athrvchvn/TLMMS/docs/handbook/chapters/ch10_security_model.tex

%% Chapter 10 — Security Model
\chapter{Security Model}
\label{ch:security}

\section{Threat Model}

MMS V2 is deployed in a university lab on a trusted LAN. The threat model assumes:

\begin{itemize}[leftmargin=1.5em]
    \item \textbf{Insider threat (student)}: A student may attempt to use a machine they are not authorised for. A student may attempt to stay on a machine beyond the session limit.
    \item \textbf{Card theft or loss}: A student's RFID card may be stolen or lost. The attacker would attempt to use it to gain machine access.
    \item \textbf{Card forgery}: An attacker may attempt to create a fake RFID card with crafted block data.
    \item \textbf{Physical access to node}: An attacker may attempt to physically tamper with the ESP32 node.
    \item \textbf{WiFi LAN attacker}: An attacker on the same WiFi may attempt to inject MQTT messages.
\end{itemize}

\textbf{Out of scope}: Remote internet attackers (Firebase security rules handle this), state-level adversaries, physical break-ins.

\section{Security Controls}

\section{Attack Surface}

\begin{longtable}{L{3.5cm}L{5cm}L{5.5cm}}
\toprule
\textbf{Surface} & \textbf{Primary risk} & \textbf{Control} \\
\midrule
\endhead
RFID card & Lost card, cloned card, modified permissions & Per-card sector key, revocation list, coordinator incident process \\
ESP32 node & Flash extraction, relay tampering, malicious firmware & Physical enclosure, secrets discipline, OTA gate, relay-off boot default \\
MQTT LAN & Command injection, status spoofing, message sniffing & Lab network trust boundary; enable authentication and ACLs for hardened deployment \\
Raspberry Pi & Firebase Admin SDK compromise, bridge outage & Least shared access, systemd watchdog, SD backup, health endpoint \\
Firebase & Admin account takeover, rule misconfiguration & Firebase Auth, Firestore role documents, sessions write locked to Admin SDK \\
Kiosk station & Unauthorized card issuance & Restrict physical access, keep master key off shared drives, audit issued cards \\
\bottomrule
\caption{MMS V2 attack surface review}
\label{tab:attack_surface}
\end{longtable}

\subsection{Card Forgery Prevention}

Each card's Sector 1 is protected by a unique 6-byte key derived as:
\[
\text{sector\_key}[6] = \text{HMAC-SHA256}(\text{master\_key},\, \text{uid\_hex})[0..5]
\]

An attacker cannot read Sector 1 data without knowing the master key. An attacker cannot write to Sector 1 without the sector key. Since the sector key is derived from the card's own UID and the master key, creating a forged card with a new UID requires knowledge of the master key.

The MFRC522 \textbf{never returns Key A on a read} --- even with authenticated access. So compromising one card does not reveal the sector key for another card.

\subsection{MIFARE Classic and Crypto-1 Limitations}

MMS V2 uses MIFARE Classic 1K cards because they are inexpensive, widely available, and supported by the MFRC522 reader used in the deployed hardware. This choice has a known security cost: MIFARE Classic uses the Crypto-1 stream cipher, which is publicly broken. A determined attacker with the right tools can recover keys or clone cards more easily than they could with modern smart-card technology.

The V2 card design reduces casual forgery by deriving a unique sector key from the card UID and a private master key. This prevents a student from simply editing visible card data with default keys. It does \textbf{not} make MIFARE Classic cryptographically strong. A high-skill attacker with physical access to a valid card and time to attack Crypto-1 remains in scope as a residual risk.

\begin{riskbox}{Security Boundary}
Treat MIFARE Classic cards as a practical lab-access token, not a high-assurance identity credential. The system is appropriate for supervised workshop access control. It should not be reused for payments, room access, hostel access, exam identity, or other high-value authorization.
\end{riskbox}

\subsection{Card Cloning Risk}

Card cloning can happen in two ways:
\begin{itemize}[leftmargin=1.5em]
    \item \textbf{UID cloning}: some magic cards can emulate another card UID. If the attacker also has valid Sector 1 contents, the node may treat the clone as the original card.
    \item \textbf{Sector recovery}: Crypto-1 attacks may recover the sector key for a card, allowing its protected data to be copied.
\end{itemize}

Mitigations are operational as much as technical: revoke lost cards quickly, keep cards physically controlled, do not publish the master key, and review suspicious repeated sessions. For high-value machines or unsupervised labs, migrate to DESFire before relying on card-only access.

\subsection{Revocation}

Lost or stolen cards are revoked via the web app. Revocation propagates to all nodes via MQTT within seconds. Revoked card UIDs are stored in LittleFS on each node, so revocation works even if the MQTT broker goes down (until the next reconnect, nodes use their cached revocation list).

\textbf{Limitation:} A revoked card that is used while a node is offline may be accepted until the node reconnects. This is a known trade-off in favour of offline availability.

\subsection{Admin Web App}

\begin{itemize}[leftmargin=1.5em]
    \item Firebase Authentication protects admin login (email/password)
    \item Firestore security rules check \texttt{/admins/\{uid\}} and \texttt{/super\_admins/\{uid\}} on every client request
    \item Sessions collection has \texttt{allow write: if false} --- only the bridge (Admin SDK) can write sessions, preventing session forgery from the client
    \item Super admin privileges required for OTA and admin management
\end{itemize}

\subsection{MQTT Security}

In the default deployment, MQTT uses \texttt{allow\_anonymous true}. This is acceptable in a physically secure lab LAN where all connected devices are managed. For hardened deployments:

\begin{itemize}[leftmargin=1.5em]
    \item Enable MQTT password authentication (see Section~\ref{sec:mqtt_auth})
    \item Add per-node ACLs to restrict which topics each node can publish/subscribe to
    \item Use TLS on MQTT (port 8883) if the lab network is untrusted
\end{itemize}

\subsection{Secrets Management}

Sensitive secrets are never committed to version control. The \texttt{.gitignore} covers:
\begin{itemize}[leftmargin=1.5em,noitemsep]
    \item \texttt{v2/access\_node/secrets.h} (WiFi credentials, master key)
    \item \texttt{v2/kiosk\_station/station\_writer/secrets\_station.h} (master key)
    \item \texttt{v2/kiosk\_station/secrets.py} (master key)
    \item \texttt{v2/rpi\_bridge/service-account.json} (Firebase Admin SDK key)
    \item \texttt{v2/web\_app/lab-access-nexus-main/.env} (Firebase client config)
\end{itemize}

\subsection{Firmware Security}

\begin{itemize}[leftmargin=1.5em]
    \item OTA firmware is downloaded from Firebase Storage (HTTPS). \texttt{esp\_https\_ota()} validates the TLS certificate.
    \item The dual-partition OTA scheme with rollback prevents a bad firmware update from permanently bricking a node.
    \item The 30-second hardware watchdog ensures the node restarts in case of firmware hang, preventing a machine from being left in relay-ON state indefinitely.
    \item Relay GPIO is driven LOW before \texttt{pinMode(OUTPUT)}, ensuring the relay is OFF during boot regardless of the GPIO's default state.
\end{itemize}

\section{DESFire Migration Path}

DESFire EV2/EV3 cards provide modern mutual authentication and stronger application separation than MIFARE Classic. The migration should be treated as a hardware-and-firmware project, not a card swap.

\begin{enumerate}[leftmargin=1.5em]
    \item Select a DESFire-capable reader module and validate ESP32 library support.
    \item Define a new card application layout with separate identity and permission files.
    \item Implement dual-reader or dual-card support during transition if existing cards must keep working.
    \item Update kiosk issuance to create DESFire applications and diversify keys per card.
    \item Add a schema version gate so nodes can reject old Classic cards after the cutover date.
    \item Re-issue all active users and record the migration in the ADR table.
\end{enumerate}

\begin{table}[H]
\centering
\caption{Classic-to-DESFire migration comparison}
\begin{tabular}{L{4cm}L{4.5cm}L{5cm}}
\toprule
\textbf{Area} & \textbf{MIFARE Classic V2} & \textbf{DESFire target} \\
\midrule
Cryptography & Crypto-1, known weak & AES-based mutual authentication \\
Reader & MFRC522 & PN532, PN5180, or equivalent DESFire-capable reader \\
Card identity & UID plus protected sector data & Application/file-level credential design \\
Transition effort & Already deployed & Requires reader, firmware, kiosk, and procurement changes \\
\bottomrule
\end{tabular}
\end{table}

\section{Security Assumptions and Limitations}

\begin{table}[H]
\centering
\caption{Security Assumptions and Limitations}
\begin{tabular}{L{5cm}L{9cm}}
\toprule
\textbf{Assumption / Limitation} & \textbf{Details} \\
\midrule
Master key is secure & If the master key is stolen, all cards can be forged. The key must be stored in a password manager, not in plaintext on a shared drive. \\
Lab WiFi is trusted & MQTT uses no encryption. A packet sniffer on the same WiFi can read MQTT messages (but not master key or Firebase credentials, which are never in MQTT). \\
Revocation is not instant & Offline nodes cannot revoke cards immediately. A stolen card may work for minutes to hours if the affected node is offline. \\
Physical node security & An attacker with physical access to the ESP32 can read flash, extract master key. Epoxy potting of the PCB mitigates this. \\
PIN not verified at machine (V2) & Card tap alone is sufficient. A thief with a stolen card can use any permitted machine. Revocation is the mitigation. \\
Firebase free tier & Data stored in Google Cloud. Subject to Google's terms of service. For highly sensitive data, consider self-hosted alternatives. \\
\bottomrule
\end{tabular}
\end{table}

\section{Security Checklist for Future Maintainers}

Before deploying any change, verify:
\begin{itemize}[leftmargin=1.5em]
    \item \texttt{secrets.h}, \texttt{secrets.py}, \texttt{secrets\_station.h} are NOT committed to git (\texttt{git status} should not show them)
    \item Firestore rules still have \texttt{allow write: if false} on the \texttt{sessions} collection
    \item RTDB rules protect \texttt{nodes} and \texttt{revoked} paths from unauthenticated writes
    \item New admin accounts are added to Firestore \texttt{/admins} or \texttt{/super\_admins} only --- do not grant access by adding to Firebase Auth alone
    \item OTA firmware URL uses HTTPS (Firebase Storage URLs always do)
    \item Master key backup is current and stored securely
\end{itemize}
