athrvchvn/TLMMS/handbook2.0/media/photo_02.jpeg

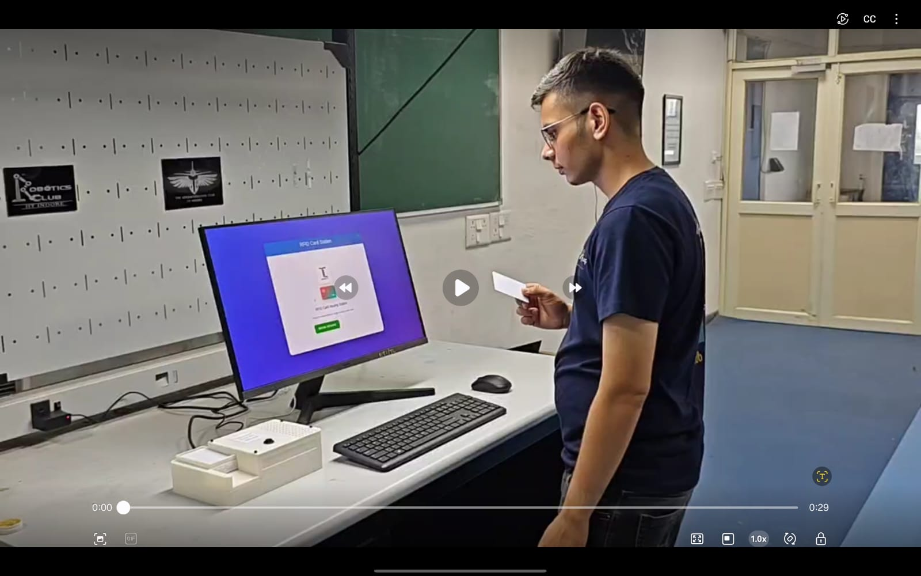
handbook2.0/media/photo_02.jpeg
