athrvchvn/TLMMS/handbook2.0/media/photo_04.jpeg

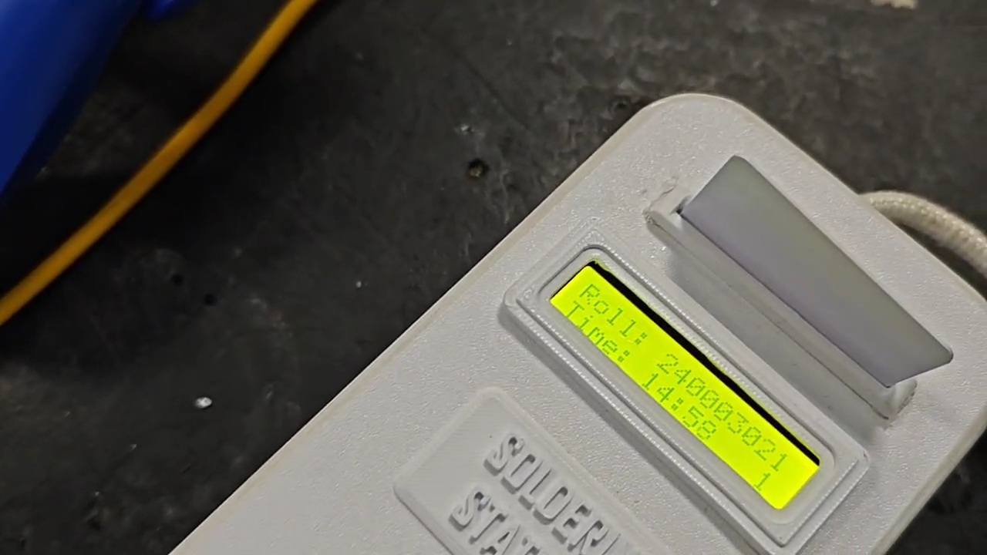
handbook2.0/media/photo_04.jpeg
