athrvchvn/TLMMS/handbook2.0/media/photo_06.jpeg

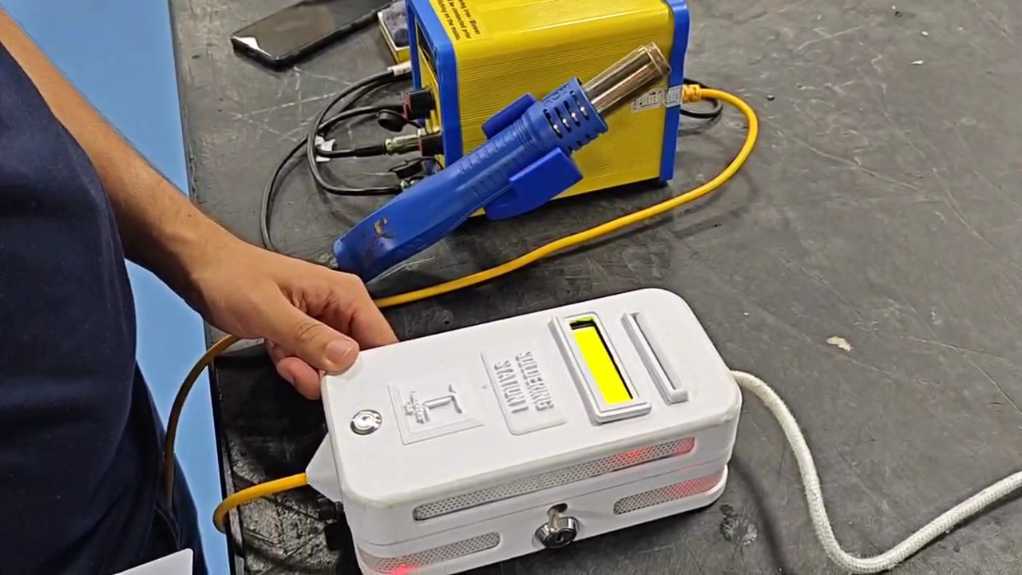
handbook2.0/media/photo_06.jpeg
