athrvchvn/TLMMS/handbook2.0/media/photo_07.jpeg

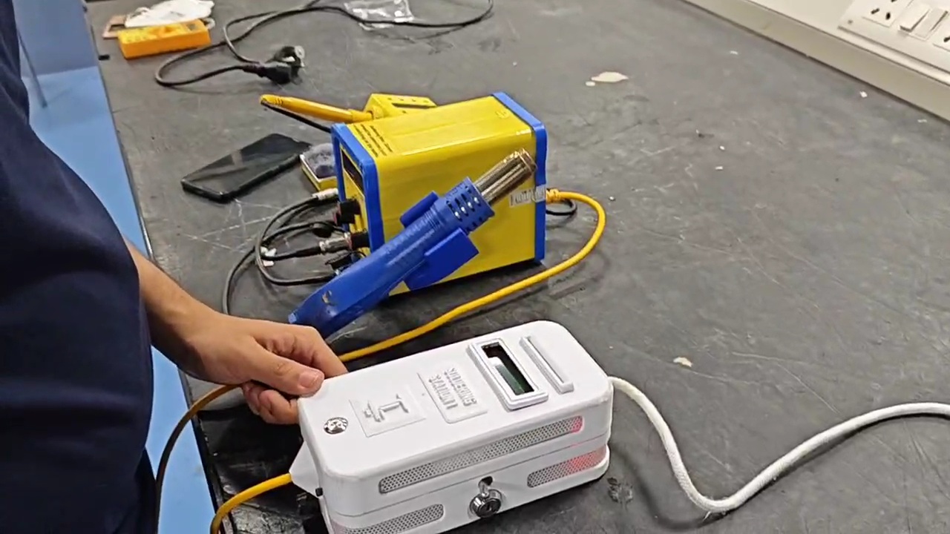
handbook2.0/media/photo_07.jpeg
