athrvchvn/TLMMS/handbook2.0/media/photo_08.jpeg

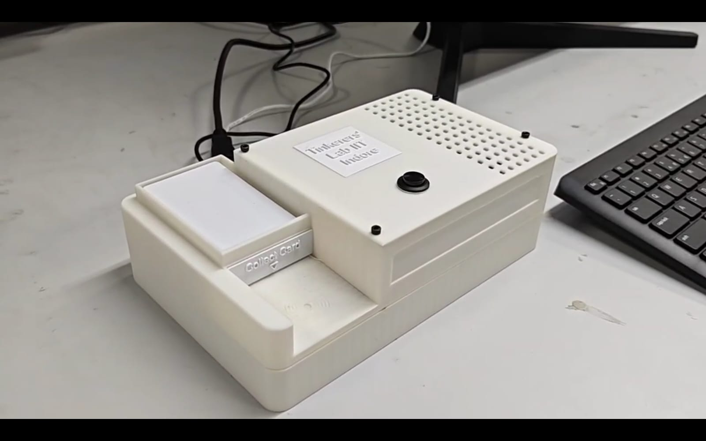
handbook2.0/media/photo_08.jpeg
