athrvchvn/TLMMS/v1/access_node/firmware/test_sketches/display/oled32_i2c_test/oled32_i2c_test.ino

#include <Wire.h>
#include <Adafruit_GFX.h>
#include <Adafruit_SSD1306.h>

#define SCREEN_WIDTH 128
#define SCREEN_HEIGHT 32

Adafruit_SSD1306 display(SCREEN_WIDTH, SCREEN_HEIGHT, &Wire, -1);

void setup() {
-
  Serial.begin(115200);

  if(!display.begin(SSD1306_SWITCHCAPVCC, 0x3C)) {
    Serial.println("OLED not found");
    while(true);
  }

  display.clearDisplay();

  display.setTextSize(1);
  display.setTextColor(SSD1306_WHITE);

  display.setCursor(0,0);
  display.println("OLED TEST");

  display.setCursor(0,10);
  display.println("ESP32 Working");

  display.setCursor(0,20);
  display.println("128x32 Display");

  display.display();
}

void loop() {

}
