athrvchvn/TLMMS/v1/access_node/firmware/test_sketches/display/oled64_spi_test/oled64_spi_test.ino

#include <SPI.h>
#include <Adafruit_GFX.h>
#include <Adafruit_SSD1306.h>

#define SCREEN_WIDTH 128
#define SCREEN_HEIGHT 64

#define OLED_MOSI 23
#define OLED_CLK 18
#define OLED_DC 16
#define OLED_CS 5
#define OLED_RESET 17

Adafruit_SSD1306 display(SCREEN_WIDTH, SCREEN_HEIGHT,
  &SPI, OLED_DC, OLED_RESET, OLED_CS);

void setup() {
  display.begin(SSD1306_SWITCHCAPVCC);
  display.clearDisplay();

  display.setTextSize(2);
  display.setTextColor(SSD1306_WHITE);
  display.setCursor(10,20);
  display.println("Hello");
  display.display();
}

void loop() {}
