athrvchvn/TLMMS/v1/access_node/firmware/test_sketches/slot_sensor/slot_sensor_test/slot_sensor_test.ino

#define SLOT_SENSOR 12   // signal pin

void setup() {
  Serial.begin(115200);
  pinMode(SLOT_SENSOR, INPUT);
}

void loop() {

  int sensorState = digitalRead(SLOT_SENSOR);

  if(sensorState == HIGH)
  {
    Serial.println("Object Detected (slot blocked)");
  }
  else
  {
    Serial.println("No Object");
  }

  delay(200);
}
